jazzmonger/LTC2983_Temp_Module/Demo Circuit Board/DC2209A1-PDF/DC2209A1-BS.pdf

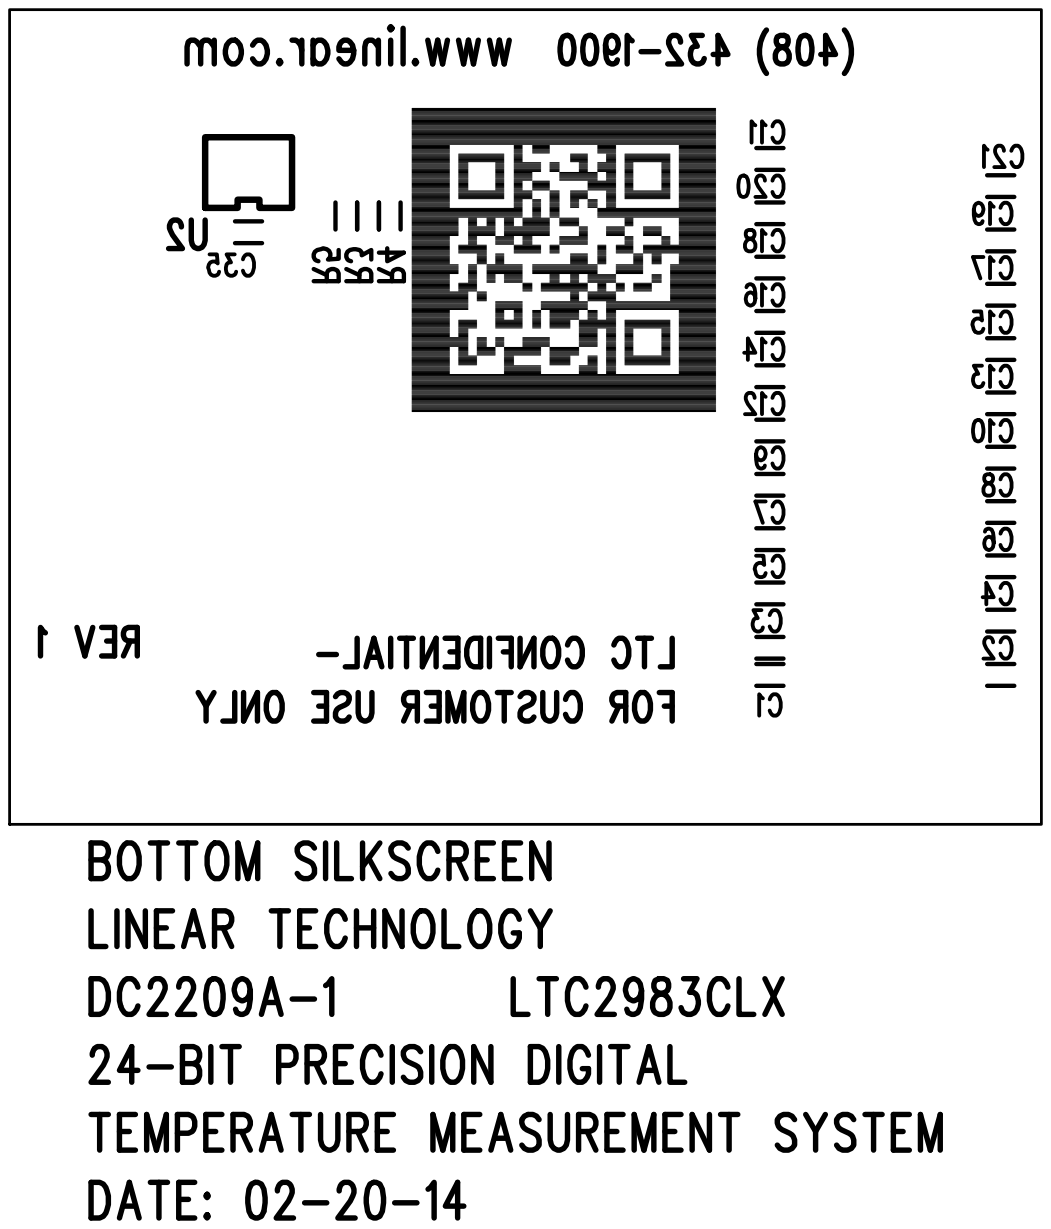
[picture p12: page 1]
