jazzmonger/LTC2983_Temp_Module/Demo Circuit Board/DC2209A1-PDF/DC2209A1-FAB.pdf

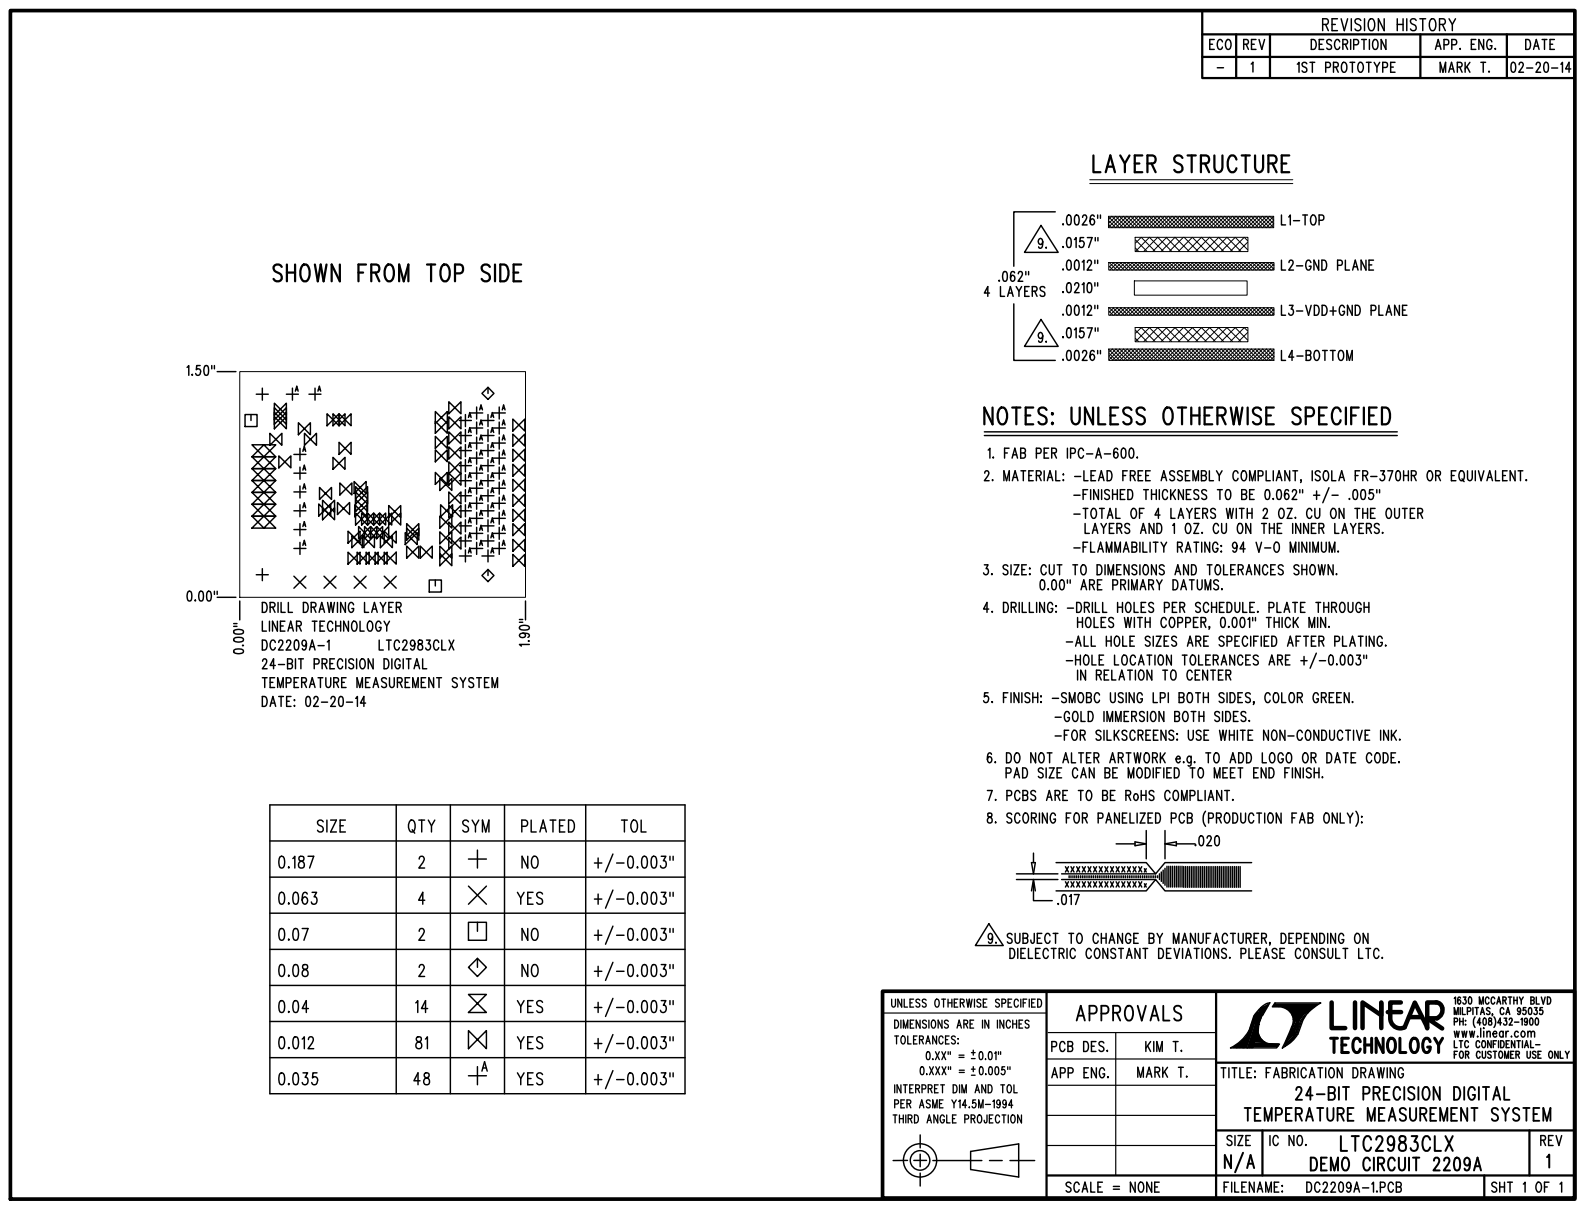
[picture p13: page 1]
