jazzmonger/LTC2983_Temp_Module/Demo Circuit Board/DC2209A1-PDF/DC2209A1-TM.pdf

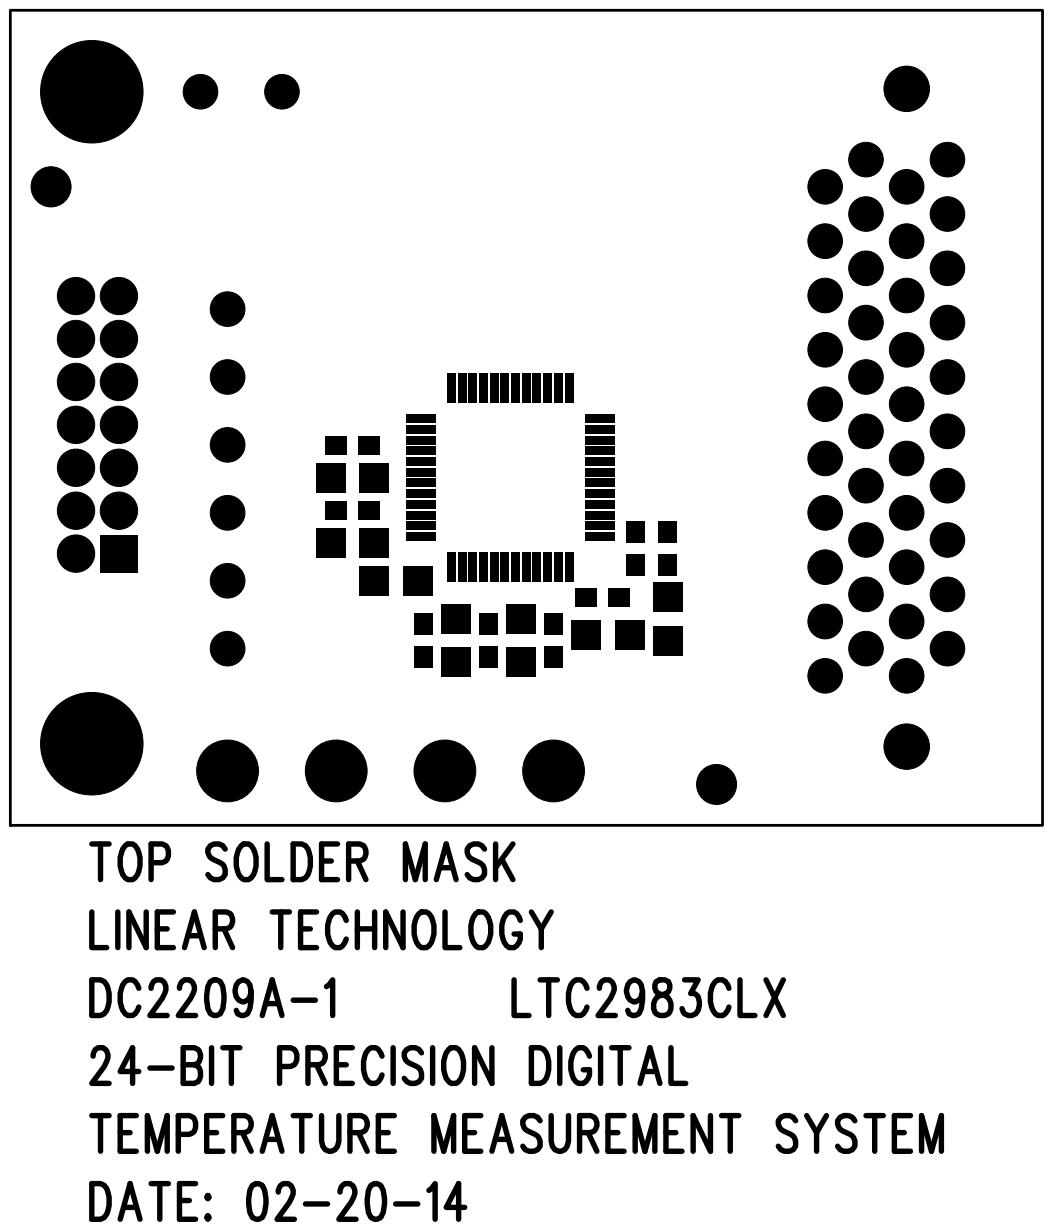
[picture p14: page 1]
