jazzmonger/LTC2983_Temp_Module/Demo Circuit Board/DC2209A1-PDF/DC2209A1-TP.pdf

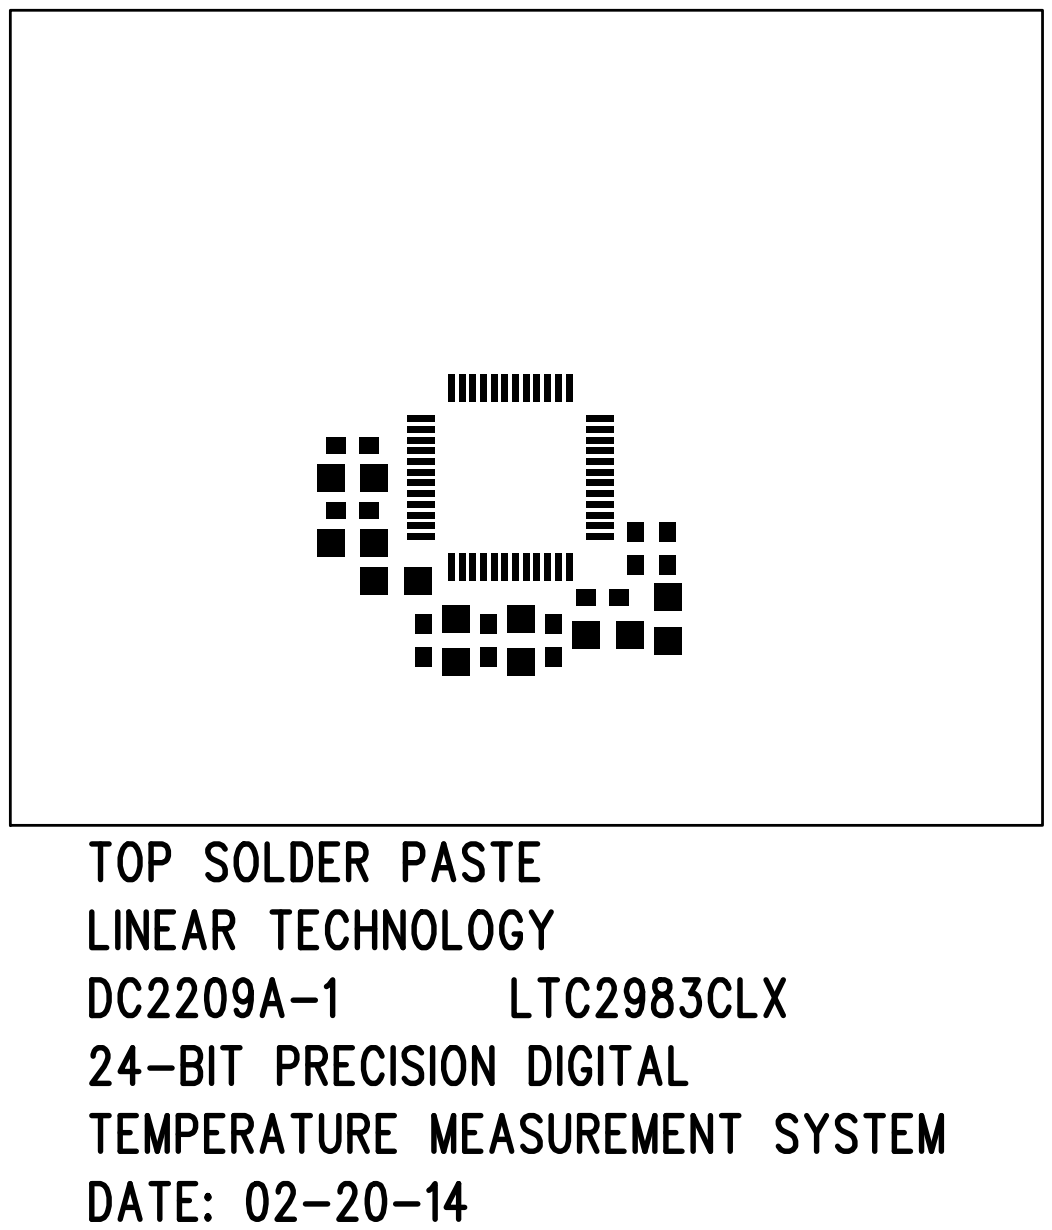
[picture p15: page 1]
