jazzmonger/LTC2983_Temp_Module/Demo Circuit Board/DC2209A1-PDF/DC2209A1-TS.pdf

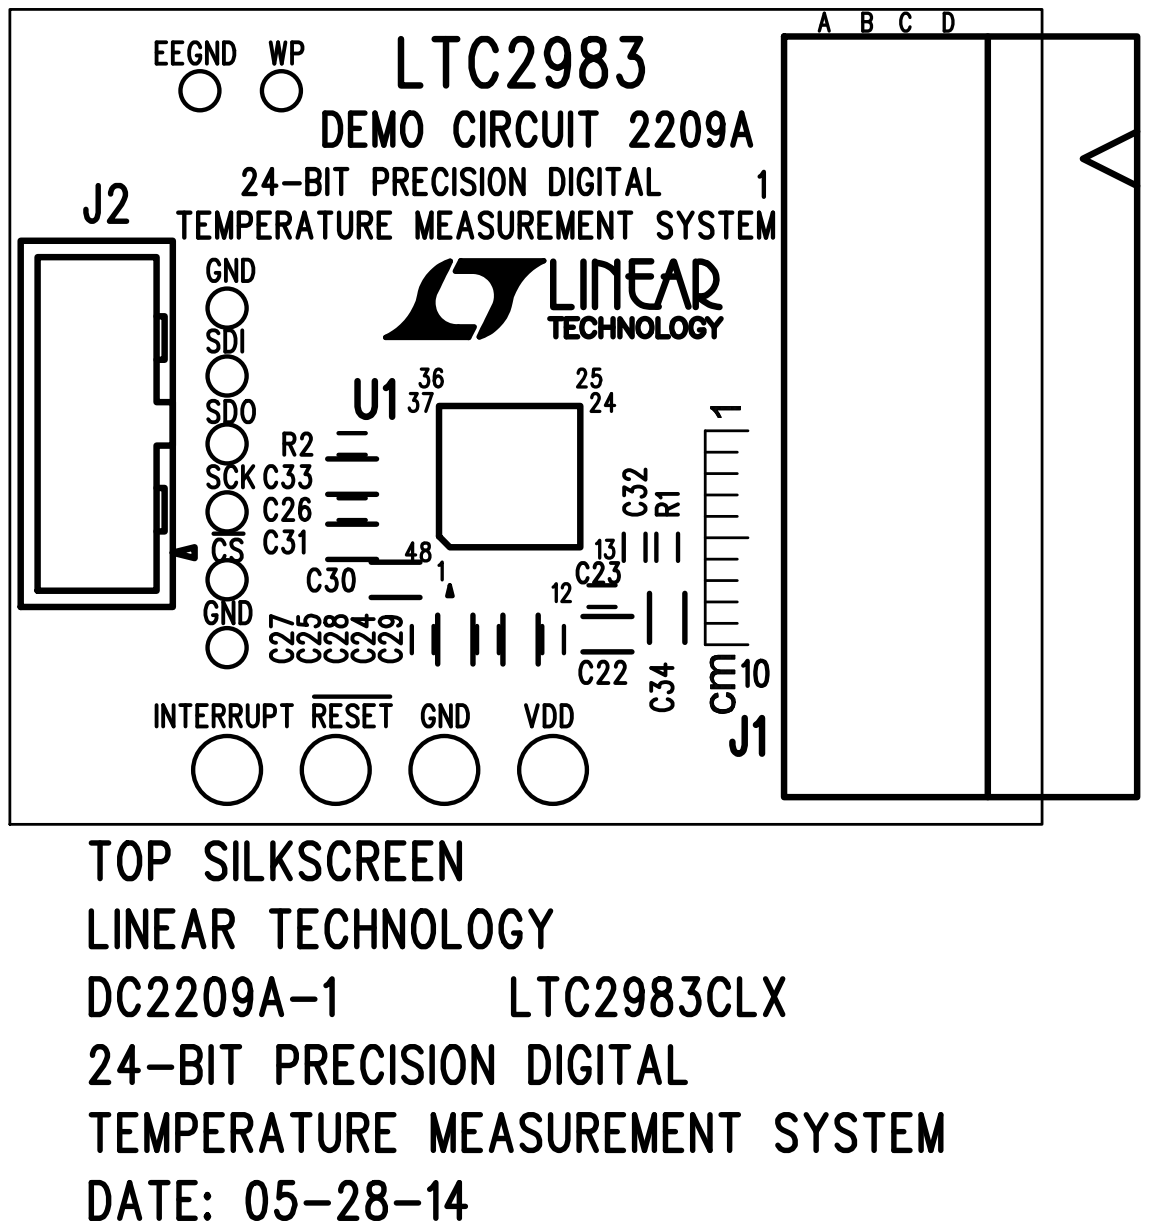
[picture p16: page 1]
